kallikak/EuroDrum/Pics/IMG_0161.jpeg

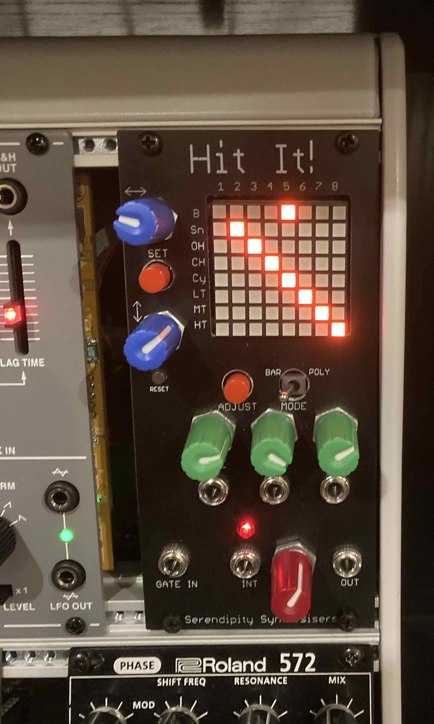
Pics/IMG_0161.jpeg
