kallikak/EuroDrum/Pics/IMG_0162.jpeg

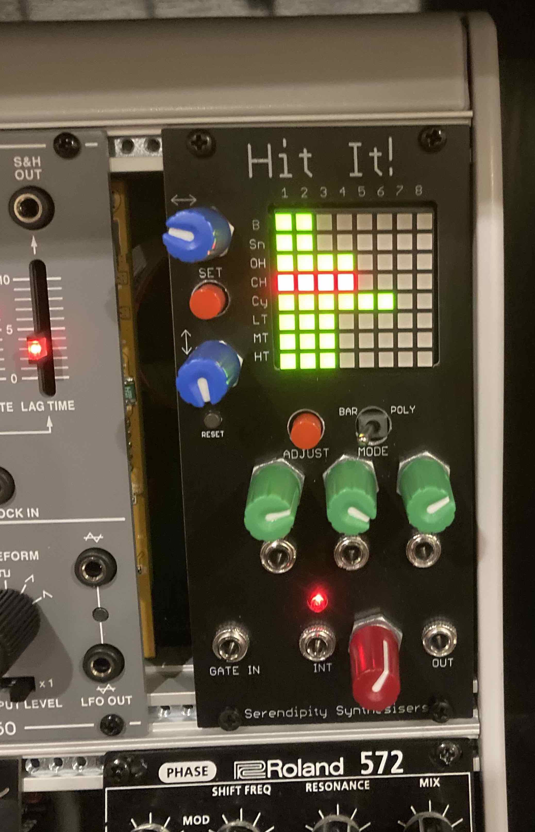
Pics/IMG_0162.jpeg
