kallikak/EuroDrum/Code/drum_samples.cpp

// Audio data converted from WAV file by wav2sketch
#include "drum_defs.h"
#include "drum_samples.h"

static uint8_t default_levels[] = {2, 4, 4, 4, 6, 3, 3, 3};
static uint8_t drum_levels[] = {2, 4, 4, 4, 6, 3, 3, 3};

static uint8_t altmask = false;

#define NUMKITS 7
static uint8_t kitmasks[NUMKITS] = {
  0b00000000,   // B,Sn,OH,CH,C,LT,MT,HT    Default kit
  0b00001111,   // B,Sn,OH,CH,RC,LC,MC,HC   Conga kit
  0b00110000,   // B,Sn,M,CV,C,LT,MT,HT     Mixed snare kit - toms
  0b01110000,   // B,RS,M,CV,C,LT,MT,HT     Mixed rimshot kit - toms
  0b00110111,   // B,Sn,M,CV,C,LC,MC,HC     Mixed snare kit - congas
  0b01110111,   // B,RS,M,CV,C,LC,MC,HC     Mixed rimshot kit - congas
  0b11111111,   // CL,RS,M,CV,RC,LC,MC,HC   Percussion kit
};

void setAltMask(uint8_t altsamples)
{
  altmask = altsamples;
}

uint8_t getAltMask()
{
  return altmask;
}

int numKits()
{
  return NUMKITS;
}

void setKit(int kit)
{
  if (kit >= 0 && kit < NUMKITS)
    altmask = kitmasks[kit];
}

uint8_t getLevel(int type)
{
  uint8_t lvl = drum_levels[type];
  if (lvl > 8)
    lvl = 8;
  return lvl;
}

void adjLevel(int type, int d)
{
  uint8_t lvl = drum_levels[type] + d;
  if (drum_levels[type] == 0 && d < 0)
    lvl = 0;
  else if (lvl > 8)
    lvl = 8;
  drum_levels[type] = lvl;
}

void setLevel(int type, uint8_t lvl)
{
  if (lvl > 8)
    lvl = 8;
  drum_levels[type] = lvl;
}

void setDefaultLevels()
{
  for (int i = 0; i < 8; ++i)
    drum_levels[i] = default_levels[i];
}

// for easier volume adjustment
float getVolumeFactor(int type)
{
  if (type < 0 || type > 7)
    return 1;
  return getLevel(type) * 0.5;
}

const unsigned int *getSample(int type)
{
  bool alt = altmask & (0x01 << (7 - type));
  switch (type)
  {
    case DK_BASS:
      return alt ? DK_CLAP_ARRAY : DK_BASS_ARRAY;
    case DK_SNARE:
      return alt ? DK_RIMSHOT_ARRAY : DK_SNARE_ARRAY;
    case DK_HAT_O:
      return alt ? DK_MARACAS_ARRAY : DK_HAT_O_ARRAY;
    case DK_HAT_C:
      return alt ? DK_CLAVES_ARRAY : DK_HAT_O_ARRAY;
    case DK_CYMBAL:
      return alt ? DK_RIDECYMBAL_ARRAY : DK_CYMBAL_ARRAY;
    case DK_TOM_L:
      return alt ? DK_CONGA_L_ARRAY : DK_TOM_L_ARRAY;
    case DK_TOM_M:
      return alt ? DK_CONGA_M_ARRAY : DK_TOM_M_ARRAY;
    case DK_TOM_H:
      return alt ? DK_CONGA_H_ARRAY : DK_TOM_H_ARRAY;
    default:
      return DK_BASS_ARRAY;
  }
}

// Converted from 01-BassDrum.wav, using 44100 Hz, u-law encoding
const unsigned int AudioSampleBassdrum[1249] = {
0x01001337,0x06060606,0x29800606,0x4E4E4E48,0x46494D4E,0x31373E42,0x9E911425,0xB1AEA9A5,
0xB9B7B5B3,0xBFBDBCBA,0xC1C1C0C0,0xC1C1C1C1,0x22B5BFC0,0x4B49453F,0x4F4E4E4C,0x50505050,
0x50505050,0x51515151,0x51515151,0x51515151,0x52525252,0x51515151,0x50505051,0x4F4F5050,
0x4D4D4E4E,0x4A4B4C4C,0x4848494A,0x45464647,0x42434344,0x3D3F4041,0x3637393B,0x2C303233,
0x19202428,0x978D0210,0xABA7A39E,0xB5B3B1AF,0xBAB9B8B6,0xBCBCBCBB,0xB9BBBBBC,0xAFB3B5B8,
0x0894A2AA,0x3631291F,0x4643403C,0x504E4B48,0x55545251,0x59585756,0x5D5C5B5A,0x605F5F5E,
0x61616160,0x62626262,0x63636363,0x64646464,0x65656464,0x65656565,0x65656565,0x66666666,
0x65666666,0x65656565,0x64656565,0x64646464,0x63636364,0x62626363,0x61616262,0x60606161,
0x5F5F6060,0x5C5D5D5E,0x595A5B5B,0x56575859,0x53545556,0x50515253,0x4A4C4E4F,0x44464749,
0x3D404143,0x3235373A,0x22262B2F,0x810D141D,0x9C97948B,0xA3A1A19F,0xA3A3A3A3,0x9EA0A1A2,
0x8B919699,0x19130A00,0x2926231F,0x3432302D,0x3B393735,0x41403E3C,0x44434241,0x46464544,
0x49484847,0x4B4B4A4A,0x4D4D4C4C,0x4E4E4E4D,0x4D4D4D4D,0x4C4C4C4C,0x4A4B4B4B,0x4849494A,
0x46474748,0x43444546,0x41424243,0x3B3D3F40,0x3436383A,0x292E3033,0x111A2125,0xA1999000,
0xB2B0ABA6,0xBCBAB7B5,0xC3C2C1BF,0xC9C7C6C4,0xCECDCBCA,0xD1D1D0CF,0xD4D3D3D2,0xD7D6D5D5,
0xD9D9D8D7,0xDBDBDADA,0xDEDDDDDC,0xE0DFDFDE,0xE0E0E0E0,0xE1E1E1E1,0xE2E2E2E1,0xE2E2E2E2,
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
0x00000000,0x00000000,0x00000000,0x00000000,0x00000000,0x00000000,0x00000000,0x00000000,
0x00000000,0x00000000,0x00000000,0x00000000,0x00000000,0x00000000,0x00000000,0x00000000,
0x00000000,0x00000000,0x00000000,0x00000000,0x00000000,0x00000000,0x00000000,0x00000000,
0x00000000,
};
